jamesmendel/terra-nova/Firmware/Terra/include/config.h

// config.h
#ifndef CONFIG_H
#define CONFIG_H

const double startLat = 52.3731313;
const double startLon = 4.8768349;

const double stopLats[] = { 52.3719817, 52.3704587, 52.3687643, 52.3668867, 52.3652726, 52.3673681, 52.3695644, 52.3710206, 52.3731313 };
const double stopLons[] = { 4.8788037, 4.8816387, 4.8841152, 4.8866618, 4.8831049, 4.8800326, 4.8773328, 4.8749497, 4.8768349 };

const int numberOfStops = 9;

#endif  // CONFIG_H
