jamesmendel/terra-nova/Firmware/Terra/src/haptics.cpp

#include <Arduino.h>
#include "haptics.h"

// Private prototypes
void _triggerPlayback();

/**
 * @brief Initializes the haptic hardware and driver.
 * 
 */
void initHaptics() {
    pinMode(PIN_HAP_IN_TRIG, OUTPUT);
    digitalWrite(PIN_HAP_IN_TRIG, LOW);

    if (!drv.begin()) {
        printf("Could not find DRV2605.\n");
        return;
    }
    drv.selectLibrary(1);
    drv.setMode(DRV2605_MODE_EXTTRIGEDGE);
    printf("Initialized DRV2605!\n");
}

/**
 * @brief Loads one effect and plays it.
 * 
 * @param effect waveform number [0 to 123]
 */
void playEffect(uint8_t effect) {
    if(effect > HAP_MAX_EFFECT_NUM) return;
    
    drv.setWaveform(0, effect);
    drv.setWaveform(1, HAP_EFFECT_STOP);

    _triggerPlayback();
}

/**
 * @brief Loads up to 8 effects and plays them in sequence.
 * 
 * @param effects Array of effect indicies [0 to 123]
 * @param len Length of array (max 8)
 */
void playEffectSequence(uint8_t *effects, uint8_t len) {
    if(len == 0 || len > HAP_MAX_SEQUENCE_NUM) return;
    
    for(uint8_t i = 0; i < len; i++) {
        drv.setWaveform(i, effects[i]);
    }

    if(len < HAP_MAX_SEQUENCE_NUM) {
        drv.setWaveform(len-1, HAP_EFFECT_STOP);
    }

    _triggerPlayback();
}

/**
 * @brief Gets state of haptic driver.
 * 
 * @return true haptics are playing
 * @return false haptics are finished
 */
bool isEffectPlaying() {
    return (drv.readRegister8(DRV2605_REG_GO) & 0x01);
}

/**
 * @brief Triggers haptic playback.
 * 
 */
void _triggerPlayback() {
    // 7.3.5.6.2: The pulse width should be at least 1 μs to ensure detection.
    digitalWrite(PIN_HAP_IN_TRIG, HIGH);
    usleep(2);
    digitalWrite(PIN_HAP_IN_TRIG, LOW);
}
